omaralabed/LivCast-Capture/refs/antmicro-sdi-mipi-bridge/sdi-mipi-bridge-hw/img/sdi-mipi-bridge.jpg

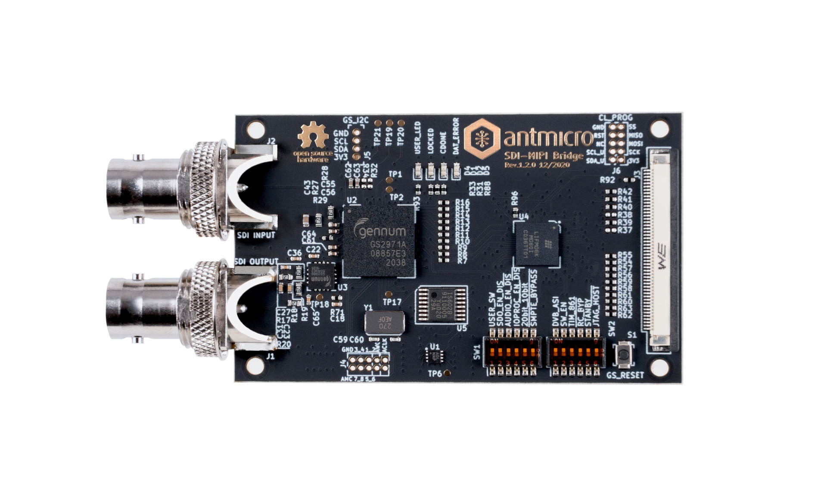
refs/antmicro-sdi-mipi-bridge/sdi-mipi-bridge-hw/img/sdi-mipi-bridge.jpg
