omaralabed/LivCast-Capture/refs/antmicro-sdi-mipi-bridge/sdi-mipi-bridge-hw/assets/previews/stackup.webp

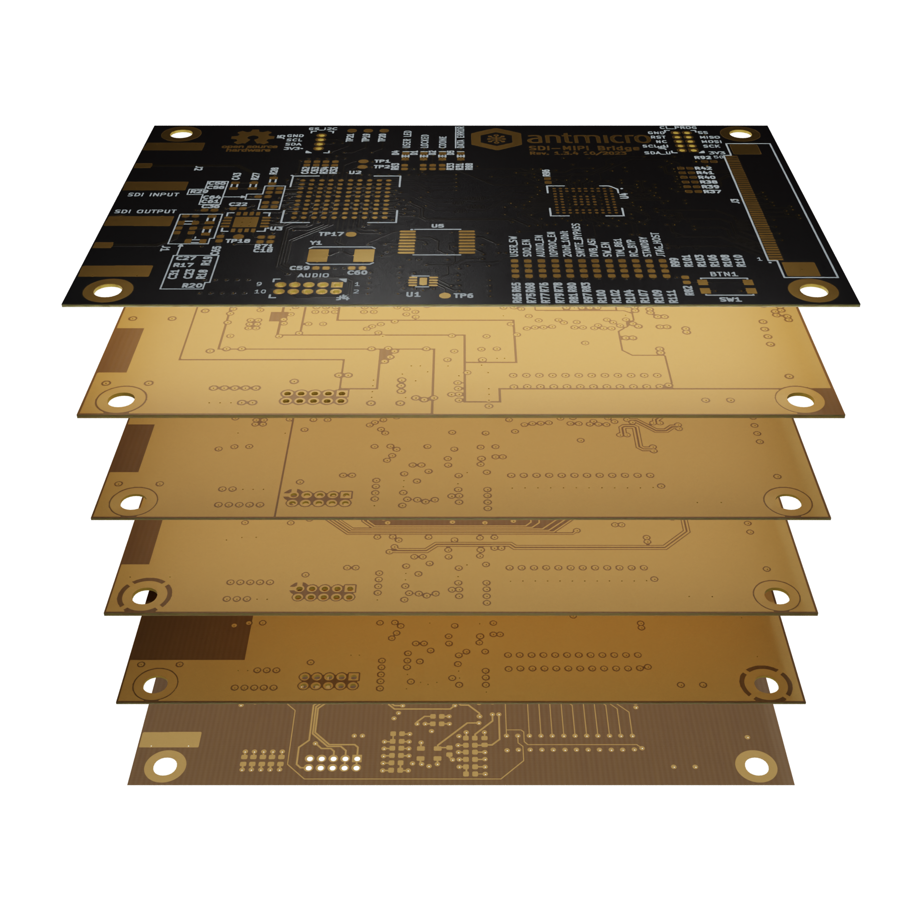
refs/antmicro-sdi-mipi-bridge/sdi-mipi-bridge-hw/assets/previews/stackup.webp
