omaralabed/LivCast-Capture/kicad/preview/LivCast_Capture_BLOCK.png

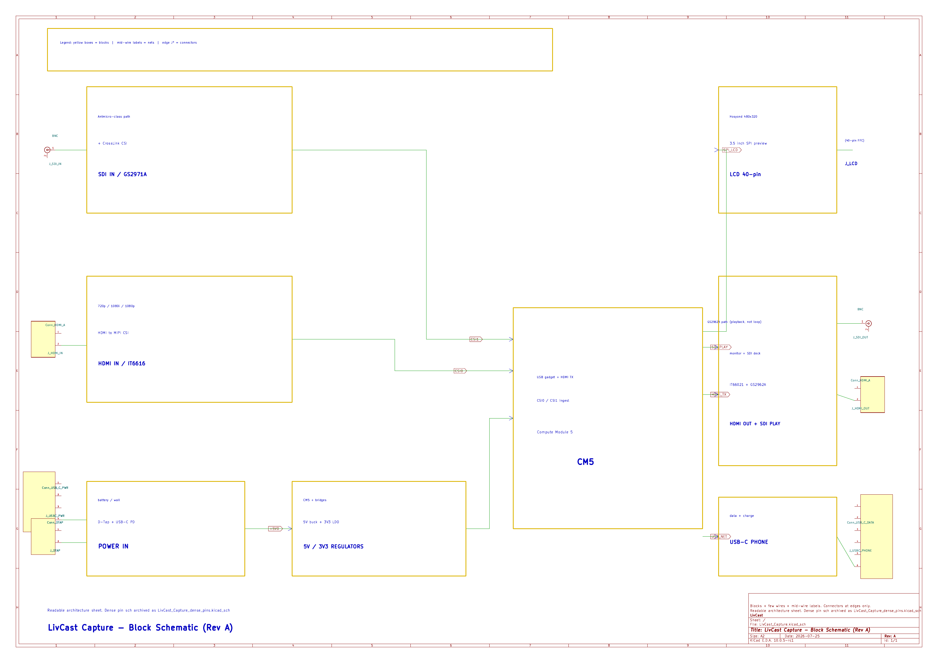
kicad/preview/LivCast_Capture_BLOCK.png
