omaralabed/LivCast-Capture/refs/antmicro-sdi-mipi-bridge/sdi-mipi-bridge-hw/assets/previews/layer1.png

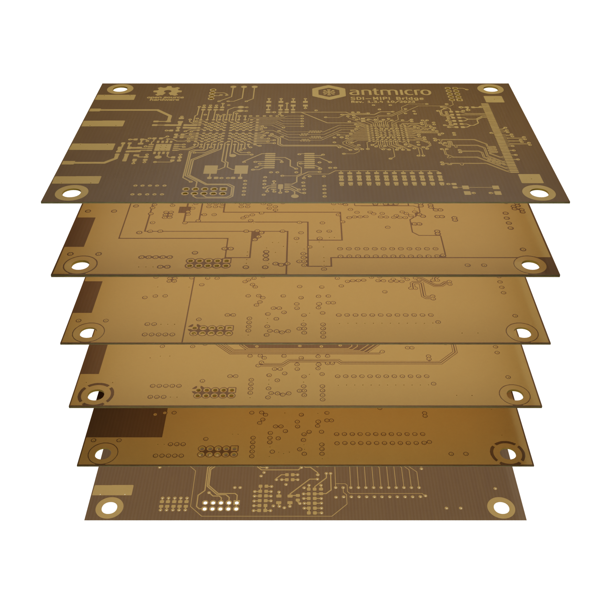
refs/antmicro-sdi-mipi-bridge/sdi-mipi-bridge-hw/assets/previews/layer1.png
