omaralabed/LivCast-Capture/refs/antmicro-sdi-mipi-bridge/sdi-mipi-bridge-hw/assets/previews/layer2_thumbnail.png

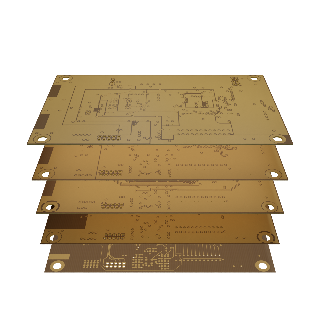
refs/antmicro-sdi-mipi-bridge/sdi-mipi-bridge-hw/assets/previews/layer2_thumbnail.png
