omaralabed/LivCast-Capture/refs/antmicro-sdi-mipi-bridge/sdi-mipi-bridge-hw/assets/previews/layer3.png

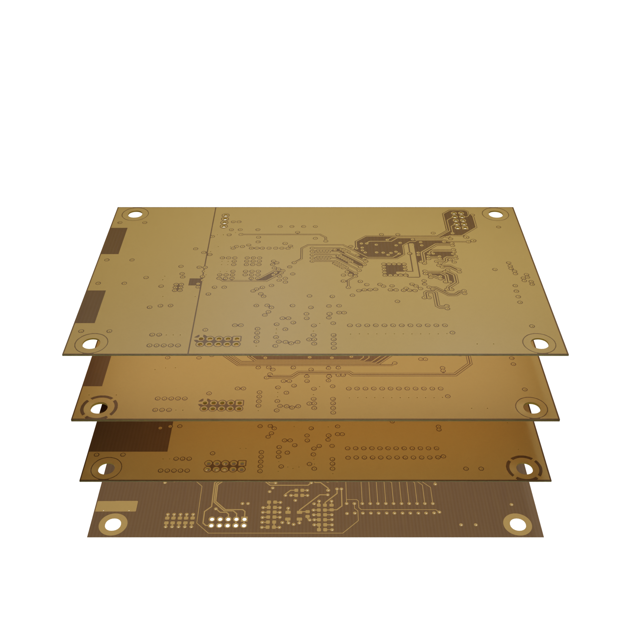
refs/antmicro-sdi-mipi-bridge/sdi-mipi-bridge-hw/assets/previews/layer3.png
