omaralabed/LivCast-Capture/refs/antmicro-sdi-mipi-bridge/sdi-mipi-bridge-hw/img/SDI_dimensions.png

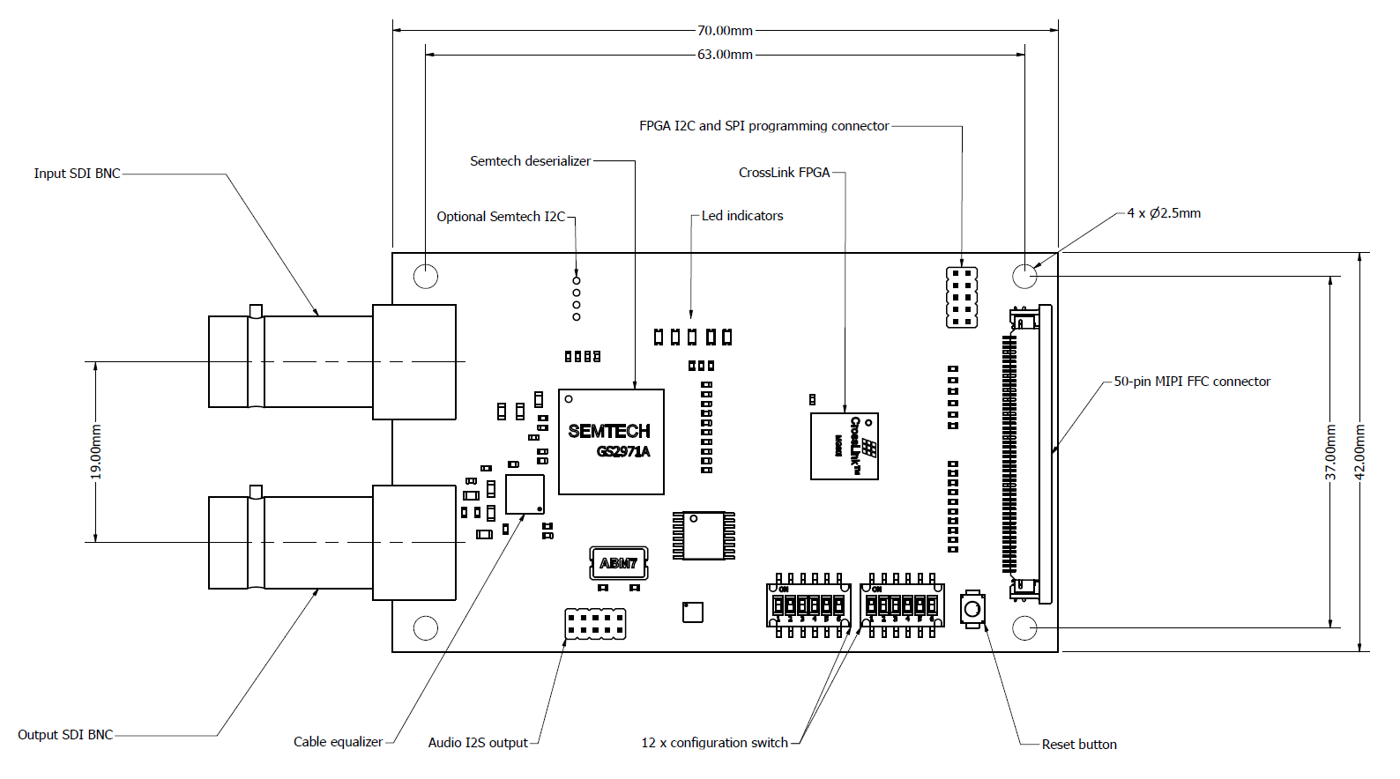
refs/antmicro-sdi-mipi-bridge/sdi-mipi-bridge-hw/img/SDI_dimensions.png
