omaralabed/LivCast-Capture/kicad/archive_sheets/LivCast_Capture_dense_pins.kicad_sch

## KiCad design kicad/archive_sheets/LivCast_Capture_dense_pins.kicad_sch (2026-07-25, an earlier design)

Schematic: LivCast_Capture_dense_pins.kicad_sch

Parts:
J101: Conn_DTAP
J102: Conn_USB_C_PWR
J103: Conn_USB_C_DATA
J201: Conn_HDMI_A
J501: Conn_BNC_031-70526-21
U101: TPS25751D
U102: LM76003
U103: TPS62130A
U201: CM5_PWR
U202: CM5_HDMI
U203: CM5_CSI0
U204: CM5_CSI1
U205: CM5_CTRL
U301: TMDS_BUF_1TO2
U401: IT66021FN
U501: GS2962A

Connections:
+1V2: U401.20 (VS), U501.21 (VDD_A_3V3), U501.24 (GND2)
+1V8: U401.21 (DE)
+3V3: U101.3 (CC2), U103.8 (PG), U301.2 (IN_D0_N), U401.22 (VDD33), U501.22 (VDD_CD), U501.23 (GND1)
+5V: U102.8 (PG), U103.5 (SS), U201.6 (GND_3), U201.7 (USB_DP), U201.8 (USB_DN)
+5V_HDMI: J201.3 (D1_P), U401.5 (RX2_P)
BIT20_10: U501.9 (RATE_SEL0)
BOOT_3V3: U103.6 (SW)
BOOT_5V: U102.6 (SW)
BUCK33_EN: U103.4 (FB)
BUCK_EN: U102.4 (FB)
CC1_DATA: J103.3 (USB_DN)
CC1_PWR: J102.3 (CC2), U101.6 (I2C_SDA)
CC2_DATA: J103.2 (USB_DP)
CC2_PWR: J102.2 (CC1), U101.5 (VIN_3V3)
CSI0_CK_N: U203.1 (CSI0_D0_P)
CSI0_CK_P: U203.2 (CSI0_D0_N)
CSI0_D0_N: U203.9 (CSI0_CK_P)
CSI0_D0_P: U203.10 (CSI0_CK_N)
CSI0_D1_N: U203.7 (CSI0_D3_P)
CSI0_D1_P: U203.8 (CSI0_D3_N)
CSI0_D2_N: U203.5 (CSI0_D2_P)
CSI0_D2_P: U203.6 (CSI0_D2_N)
CSI0_D3_N: U203.3 (CSI0_D1_P)
CSI0_D3_P: U203.4 (CSI0_D1_N)
CSI1_CK_N: U204.1 (CSI1_D0_P)
CSI1_CK_P: U204.2 (CSI1_D0_N)
CSI1_D0_N: U204.9 (CSI1_CK_P)
CSI1_D0_P: U204.10 (CSI1_CK_N)
CSI1_D1_N: U204.7 (CSI1_D3_P)
CSI1_D1_P: U204.8 (CSI1_D3_N)
CSI1_D2_N: U204.5 (CSI1_D2_P)
CSI1_D2_P: U204.6 (CSI1_D2_N)
CSI1_D3_N: U204.3 (CSI1_D1_P)
CSI1_D3_P: U204.4 (CSI1_D1_N)
DVB_ASI: U501.5 (F_DE)
FB_3V3: U103.2 (EN)
FB_5V: U102.2 (EN)
GND: J101.1 (VIN), J102.1 (VBUS), J103.1 (VBUS), J201.1 (D0_P), J201.2 (D0_N), U101.4 (GND), U101.8 (PP5V), U102.3 (GND), U103.3 (GND), U201.3 (+5V_3), U201.4 (GND_1), U201.5 (GND_2), U301.1 (IN_D0_P), U401.17 (VIDEO_BUS), U401.18 (PCLK), U401.19 (HS), U501.17 (SDO), U501.18 (SDO#), U501.19 (VDD_CORE_1V2), U501.20 (VDD_IO)
GS_SDOUT: U501.3 (H_HSYNC)
GS_STANDBY#: U501.10 (RATE_SEL1)
HDMI_MON_DDC_SCL: J201.5 (D2_P)
HDMI_MON_DDC_SDA: J201.6 (D2_N)
HDMI_MON_HPD: J201.4 (D1_N)
HDMI_RX_DDC_SCL: U401.6 (RX2_N)
HDMI_RX_DDC_SDA: U401.7 (RXC_P)
HDMI_RX_HPD: U401.8 (RXC_N)
I2C_SCL: U101.1 (VBUS), U205.8 (SDI_TX_SPI_SCK), U401.2 (RX0_N)
I2C_SDA: U101.2 (CC1), U205.6 (SPI_CS), U205.7 (SDI_TX_SPI_MOSI), U205.9 (SDI_TX_SPI_CS), U401.3 (RX1_P)
IT66021_INT#: U401.1 (RX0_P)
IT66021_RESET#: U401.4 (RX1_N)
unnamed: J201.7 (CK_P), J201.8 (CK_N), J201.9 (DDC_SDA), J201.10 (DDC_SCL), J201.11 (HPD), J201.12 (+5V), J201.13 (GND), J201.14 (SHIELD), U301.20 (OUTB_D0_P), U301.21 (OUTB_D0_N), U301.22 (OUTB_D1_P), U301.23 (OUTB_D1_N), U301.24 (OUTB_D2_P), U301.25 (OUTB_D2_N), U301.26 (OUTB_CK_P), U301.27 (OUTB_CK_N)
unnamed: J501.1, U501.26 (GND4)
unnamed: U202.1 (HDMI_TX_D0_P), U301.4 (IN_D1_N)
unnamed: U202.2 (HDMI_TX_D0_N), U301.5 (IN_D2_P)
unnamed: U202.3 (HDMI_TX_D1_P), U301.6 (IN_D2_N)
unnamed: U202.4 (HDMI_TX_D1_N), U301.7 (IN_CK_P)
unnamed: U202.5 (HDMI_TX_D2_P), U301.8 (IN_CK_N)
unnamed: U202.6 (HDMI_TX_D2_N), U301.9 (OE#)
unnamed: U202.7 (HDMI_TX_CK_P), U301.10 (VDD)
unnamed: U202.8 (HDMI_TX_CK_N), U301.11 (GND)
unnamed: U301.12 (OUTA_D0_P), U401.9 (HPD)
unnamed: U301.13 (OUTA_D0_N), U401.10 (DDC_SDA)
unnamed: U301.14 (OUTA_D1_P), U401.11 (DDC_SCL)
unnamed: U301.15 (OUTA_D1_N), U401.12 (+5V_HDMI)
unnamed: U301.16 (OUTA_D2_P), U401.13 (RESET#)
unnamed: U301.17 (OUTA_D2_N), U401.14 (I2C_SDA)
unnamed: U301.18 (OUTA_CK_P), U401.15 (I2C_SCL)
unnamed: U301.19 (OUTA_CK_N), U401.16 (INT#)
unnamed: U401.23 (VDD18), U501.12 (DVB_ASI)
unnamed: U401.24 (VDD12), U501.13 (SDIN)
unnamed: U401.25 (GND1), U501.14 (SDOUT)
unnamed: U401.26 (GND2), U501.15 (SCLK)
unnamed: U401.27 (GND3), U501.16 (CS#)
PD_GPIO1: U101.9 (PPHV)
PG_3V3: U103.7 (VOUT)
PG_5V: U102.7 (VOUT)
PP5V: U101.11 (GND2)
PPHV: U101.10 (GPIO1)
RATE_SEL0: U501.8 (BIT20_10)
RATE_SEL1: U501.7 (STANDBY#)
SDI_TX_N: U501.25 (GND3)
SDI_TX_SPI_CS: U205.1 (I2C_SDA), U205.3 (SPI_MOSI), U205.4 (SPI_MISO), U501.1 (VIDEO_BUS), U501.4 (V_VSYNC)
SDI_TX_SPI_SCK: U205.2 (I2C_SCL), U501.2 (PCLK)
SDO_EN: U501.11 (SMPTE_BYPASS)
SMPTE_BYPASS: U501.6 (SDO_EN)
SPI_SCK: U205.5 (SPI_SCK)
SS_3V3: U103.1 (VIN)
SS_5V: U102.1 (VIN)
SW_3V3: U103.9 (BOOT)
SW_5V: U102.9 (BOOT)
TMDS_OE#: U301.3 (IN_D1_P)
USB_DN: J103.4 (CC1), U201.1 (+5V_1)
USB_DP: J103.5 (CC2), U201.2 (+5V_2)
VBUS: J102.4 (GND), J103.6 (GND), U101.7 (I2C_SCL)
VIN_RAW: J101.2 (GND), U102.5 (SS)

Notes on the sheet:
LivCast Capture Rev A — wire-only IC links; labels on power / region exits only
Playback row: CM5_HDMI -wires-> TMDS -OUTA wires-> HDMI mon; OUTB wires-> IT66021 -VIDEO_BUS-> GS2962 -> BNC
VIDEO_BUS = 20-bit parallel (single wire on schematic). CSI/CTRL globals pitched 15mm on long stubs.
to monitor
HDMI IN ingest - TBD (archive_sheets/03)
SDI IN ingest - TBD (archive_sheets/04, Antmicro)
